notluckydog/esp32_watch_frame/sofeware/ico/64X64/图片1.png

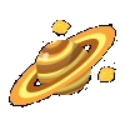
sofeware/ico/64X64/图片1.png
