notluckydog/esp32_watch_frame/sofeware/ico/太空人/R-C.gif

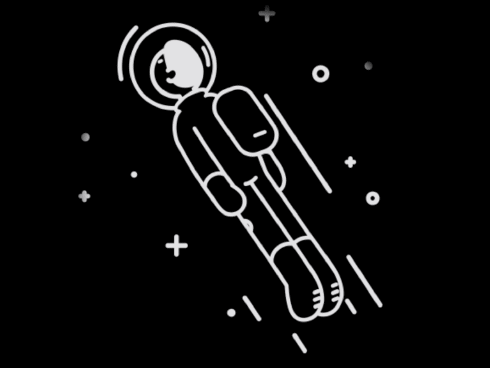
sofeware/ico/太空人/R-C.gif
