notluckydog/esp32_watch_frame/sofeware/esp32_watch/include/dinosaur_pic.h

#ifndef _DINOSAUR_PIC_H
#define _DINOSAUR_PIC_H
#include <Arduino.h>
//保存恐龙小游戏的素材

const uint16_t gImage_stop[520] = { 0X10,0X10,0X00,0X10,0X00,0X10,0X01,0X1B,
0X00,0X00,0X00,0X20,0X00,0X00,0X00,0X00,0X00,0X00,0X00,0X00,0X00,0X00,0X00,0X00,
0X00,0X00,0X00,0X00,0X00,0X00,0X00,0X00,0X00,0X00,0X00,0X00,0X00,0X20,0X00,0X00,
0X00,0X00,0X00,0X00,0X00,0X00,0X52,0X8A,0X63,0X0C,0X5A,0XEC,0X5A,0XCC,0X00,0X21,
0X00,0X21,0X5A,0XCC,0X5A,0XEC,0X63,0X0C,0X52,0X8A,0X00,0X00,0X00,0X00,0X00,0X00,
0X00,0X00,0X00,0X00,0X00,0X00,0X63,0X0C,0X5A,0XEC,0X52,0XAB,0X63,0X2D,0X00,0X00,
0X00,0X00,0X63,0X2D,0X52,0XAB,0X5A,0XEC,0X63,0X0C,0X00,0X00,0X00,0X00,0X00,0X00,
0X00,0X00,0X00,0X20,0X00,0X00,0X5A,0XEC,0X5A,0XCB,0X5A,0XEC,0X5A,0XCC,0X00,0X01,
0X00,0X01,0X5A,0XCC,0X5A,0XEC,0X5A,0XCB,0X5A,0XEC,0X00,0X00,0X00,0X20,0X00,0X00,
0X00,0X00,0X00,0X00,0X00,0X00,0X5A,0XEC,0X5A,0XEC,0X63,0X2D,0X52,0XAB,0X00,0X01,
0X00,0X01,0X52,0XAB,0X63,0X2D,0X5A,0XEC,0X5A,0XEC,0X00,0X00,0X00,0X00,0X00,0X00,
0X00,0X00,0X00,0X00,0X00,0X00,0X63,0X0C,0X52,0X8B,0X5A,0XCB,0X5A,0XEC,0X00,0X01,
0X00,0X01,0X5A,0XEC,0X5A,0XCC,0X52,0X8B,0X63,0X0C,0X00,0X00,0X00,0X00,0X00,0X00,
0X00,0X00,0X00,0X00,0X00,0X00,0X63,0X0C,0X5A,0XEC,0X62,0XEC,0X63,0X0D,0X00,0X01,
0X00,0X01,0X63,0X0D,0X62,0XEC,0X5A,0XEC,0X63,0X0C,0X00,0X00,0X00,0X00,0X00,0X00,
0X00,0X00,0X00,0X00,0X00,0X00,0X5A,0XCB,0X5A,0XCC,0X5A,0XEC,0X52,0XAC,0X00,0X01,
0X00,0X01,0X52,0XAC,0X5A,0XEC,0X5A,0XCC,0X5A,0XCB,0X00,0X00,0X00,0X00,0X00,0X00,
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
0X00,0X00,0X00,0X00,0X00,0X00,0X00,0X00,0X00,0X00,0X00,0X00,0X00,0X00,0X00,0X00,
0X00,0X00,0X00,0X00,0X00,0X00,0X00,0X00,0X00,0X00,0X00,0X00,0X00,0X00,0X00,0X00,
0X00,0X00,0X00,0X00,0X00,0X00,0X00,0X00,0X00,0X00,0X00,0X00,};

#endif
