notluckydog/esp32_watch_frame/sofeware/esp32_watch/include/pic_ico.h

#ifndef _PIC_H_
#define _PIC_H_

#include <Arduino.h>

const uint16_t gImage_black_ico[8458] = { 0X10,0X10,0X00,0X41,0X00,0X41,0X01,0X1B,
0X08,0X61,0X08,0X61,0X08,0X61,0X08,0X61,0X08,0X61,0X08,0X61,0X08,0X61,0X08,0X61,
0X08,0X61,0X08,0X61,0X08,0X61,0X08,0X61,0X08,0X61,0X08,0X61,0X08,0X61,0X08,0X61,
0X08,0X61,0X08,0X61,0X08,0X61,0X08,0X61,0X08,0X61,0X08,0X61,0X08,0X61,0X08,0X61,
0X08,0X61,0X08,0X61,0X08,0X61,0X08,0X61,0X08,0X61,0X08,0X61,0X08,0X61,0X08,0X61,
0X08,0X61,0X08,0X61,0X08,0X61,0X08,0X61,0X08,0X61,0X08,0X61,0X08,0X61,0X08,0X61,
0X08,0X61,0X08,0X61,0X08,0X61,0X08,0X61,0X08,0X61,0X08,0X61,0X08,0X61,0X08,0X61,
0X08,0X61,0X08,0X61,0X08,0X61,0X08,0X61,0X08,0X61,0X08,0X61,0X08,0X61,0X08,0X61,
0X08,0X61,0X08,0X61,0X08,0X61,0X08,0X61,0X08,0X61,0X08,0X61,0X08,0X61,0X08,0X61,
0X08,0X61,0X08,0X61,0X08,0X61,0X08,0X61,0X08,0X61,0X08,0X61,0X08,0X61,0X08,0X61,
0X08,0X61,0X08,0X61,0X08,0X61,0X08,0X61,0X08,0X61,0X08,0X61,0X08,0X61,0X08,0X61,
0X08,0X61,0X08,0X61,0X08,0X61,0X08,0X61,0X08,0X61,0X08,0X61,0X08,0X61,0X08,0X61,
0X08,0X61,0X08,0X61,0X08,0X61,0X08,0X61,0X08,0X61,0X08,0X61,0X08,0X61,0X08,0X61,
0X08,0X61,0X08,0X61,0X08,0X61,0X08,0X61,0X08,0X61,0X08,0X61,0X08,0X61,0X08,0X61,
0X08,0X61,0X08,0X61,0X08,0X61,0X08,0X61,0X08,0X61,0X08,0X61,0X08,0X61,0X08,0X61,
0X08,0X61,0X08,0X61,0X08,0X61,0X08,0X61,0X08,0X61,0X08,0X61,0X08,0X61,0X08,0X61,
0X08,0X61,0X08,0X61,0X08,0X61,0X08,0X61,0X08,0X61,0X08,0X61,0X08,0X61,0X08,0X61,
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
0XFF,0XFF,0XFF,0XFF,0XFF,0XFF,0XFF,0XFF,0XFF,0XFF,0XFF,0XFF,0XFF,0XFF,0XFF,0XFF,
0XFF,0XFF,0XFF,0XFF,0XFF,0XFF,0XFF,0XFF,0XFF,0XFF,0XFF,0XFF,0XFF,0XFF,0XFF,0XFF,
0XFF,0XFF,0XFF,0XFF,0XFF,0XFF,0XFF,0XFF,0XFF,0XFF,0XFF,0XFF,0XFF,0XFF,0XFF,0XFF,
};
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
